paclema/iot-co2Tracker/SquareLineProject/assets/1015935.png

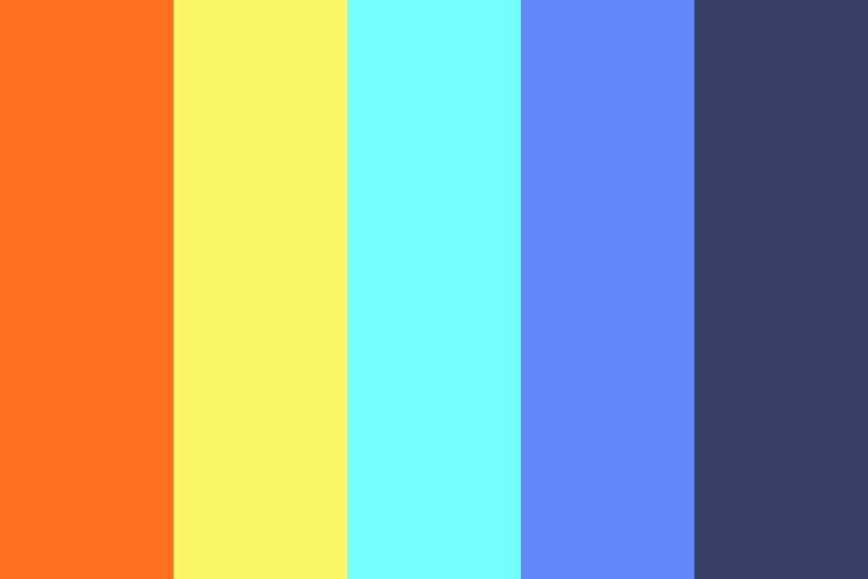
SquareLineProject/assets/1015935.png
